marucome09/24PFFCto34P_conv/kicad/fd_24ffc_to_34.sch

## KiCad design kicad/fd_24ffc_to_34.sch (2020-07-10)

Schematic: fd_24ffc_to_34.sch

Parts:
J1: Conn_02x17_Odd_Even; PinHeader_2x17_P2.54mm_Vertical
J2: Conn_01x03; PinHeader_1x03_P2.54mm_Vertical
J3: Conn_01x02; PinHeader_1x02_P2.54mm_Vertical
J4: FD_FFC_24p; Molex_52045-2445_24p
R1: R; R_Axial_DIN0207_L6.3mm_D2.5mm_P7.62mm_Horizontal
